gepid-upf/berimbau-esp32/main/caxixi.h

/**********************************************************************
* Written by WAVToCode
* Date:				Wed Apr 10 10:54:57 AM
* FileName:			caxixi.h
* Interleaved:		Yes
* Signed:			Yes
* No. of channels:	1
* No. of samples:	14392
* Bits/Sample:		16
**********************************************************************/

const uint32_t caxixi_length = 14392;

const int16_t caxixi_data[] = {
 -9, -2679, -722, 1820, -1052, -2216, 1130, 2875, // 0-7
1483, -2339, -2816, 1369, 775, -421, 490, 1471, // 8-15
1308, -1197, -1289, 709, -634, -2290, -438, 1622, // 16-23
1617, 1131, -1656, -1511, 1270, 232, 1076, 1445, // 24-31
-755, -719, 657, -1205, -3591, 828, 5721, -943, // 32-39
-6613, -3469, 251, 4771, 2240, -2296, 3304, 4577, // 40-47
511, -1909, -4525, 761, 8344, 1268, -6598, -2080, // 48-55
3356, 3432, -6528, -12416, -1171, 8881, 7654, -2114, // 56-63
-10416, -1733, 9952, 4211, -6298, -4386, 10158, 18213, // 64-71
1172, -10200, -6016, 1414, 5411, -7326, -12972, -827, // 72-79
9698, 2561, -13105, -18094, -3788, 12307, 17874, 10090, // 80-87
-3818, -5379, 6128, 17087, 5230, -15354, -18685, -1749, // 88-95
11127, 3568, -13002, -18067, -1662, 11987, 15213, -485, // 96-103
-7518, 2166, 7767, 9175, 1754, -12427, -6310, 11603, // 104-111
5318, -313, -1607, -864, 4625, -9109, -16903, 3754, // 112-119
14055, 778, -10999, -11145, 7126, 16884, -4923, -18462, // 120-127
1023, 20400, 15031, -5100, -24160, -12337, 16128, 12681, // 128-135
-10447, -10078, 1457, 14195, 17467, -12761, -19398, 9354, // 136-143
19190, 4248, -12628, -20710, -3382, 9069, -3041, -2253, // 144-151
-70, 1747, 10796, 3102, -5364, 5888, 6236, -6032, // 152-159
-81, 8112, 2155, -8550, -6823, 5008, 4467, -5425, // 160-167
-10925, -4550, 7412, 6031, -4954, -7164, -305, 7155, // 168-175
5011, -170, 141, 6229, 14437, 4639, -8979, -6459, // 176-183
-1706, -1893, 786, -7179, -15095, -3007, -1027, 805, // 184-191
12359, 997, -8763, 6834, 7046, 553, 4698, -2860, // 192-199
-5968, 8424, 13828, 512, -10433, -14140, -7256, 7053, // 200-207
5303, -2945, 3735, 4766, -2799, -1312, -1800, -3457, // 208-215
3213, 5648, 2101, 3135, -788, -9046, -5437, -785, // 216-223
3283, 7837, 1529, 163, 2595, -2160, -5274, -4466, // 224-231
-4587, 2612, 9347, 5459, -1384, -8128, -7694, 3405, // 232-239
10019, 3114, -7327, -4528, 4920, -514, -8646, -4258, // 240-247
5073, 7383, -331, -5284, -4044, 769, 8364, 5031, // 248-255
-1654, 1043, 1291, -978, -2179, -5084, 3956, 10897, // 256-263
-463, -4194, -1740, -4923, -2961, -1382, 140, 7903, // 264-271
1263, -7760, -4552, -5942, 821, 10355, 3710, 2887, // 272-279
1736, -1740, 5676, -691, -8164, -2082, -3065, -356, // 280-287
8329, 2299, -5475, -27, 4562, -2660, -5952, 984, // 288-295
4384, 2684, -2825, -7814, 573, 8458, -99, -5609, // 296-303
5021, 14547, 4639, -5656, -8726, -14209, -4368, 9500, // 304-311
3289, -4439, -2678, -2196, 4008, 6252, -3699, -7053, // 312-319
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
