gepid-upf/berimbau-esp32/main/moeda.h

/**********************************************************************
* Written by WAVToCode
* Date:				Wed Apr 10 10:55:23 AM
* FileName:			moeda.h
* Interleaved:		Yes
* Signed:			Yes
* No. of channels:	1
* No. of samples:	70588
* Bits/Sample:		16
**********************************************************************/

const uint32_t moeda_length = 70588;

const int16_t moeda_data[] = {
 96, 179, 249, 320, 383, 442, 493, 536, // 0-7
572, 607, 639, 660, 673, 676, 666, 653, // 8-15
639, 618, 587, 534, 477, 424, 371, 302, // 16-23
213, 117,  25, -58, -150, -242, -348, -449, // 24-31
-555, -660, -757, -853, -947, -1043, -1136, -1223, // 32-39
-1306, -1390, -1468, -1537, -1594, -1650, -1700, -1745, // 40-47
-1782, -1819, -1852, -1874, -1865, -1865, -1865, -1842, // 48-55
-1815, -1793, -1768, -1709, -1647, -1591, -1534, -1475, // 56-63
-1402, -1318, -1233, -1146, -1059, -977, -883, -793, // 64-71
-705, -613, -520, -417, -313, -220, -148, -69, // 72-79
 19, 111, 185, 253, 332, 402, 450, 501, // 80-87
545, 585, 609, 635, 652, 654, 657, 655, // 88-95
631, 607, 577, 546, 506, 458, 400, 337, // 96-103
284, 230, 155,  77, -14, -101, -193, -289, // 104-111
-374, -450, -526, -605, -680, -756, -832, -901, // 112-119
-955, -1006, -1053, -1092, -1129, -1162, -1191, -1209, // 120-127
-1210, -1210, -1215, -1215, -1197, -1170, -1144, -1105, // 128-135
-1059, -1007, -962, -908, -855, -793, -723, -650, // 136-143
-588, -503, -413, -330, -242, -152, -69,  18, // 144-151
105, 179, 261, 346, 417, 478, 543, 619, // 152-159
694, 748, 791, 831, 877, 937, 985, 1001, // 160-167
1014, 1022, 1025, 1010, 997, 988, 975, 943, // 168-175
899, 847, 787, 730, 680, 619, 547, 479, // 176-183
403, 330, 253, 168,  88,  17, -57, -129, // 184-191
-202, -267, -323, -363, -409, -458, -503, -543, // 192-199
-579, -608, -629, -628, -618, -615, -604, -571, // 200-207
-552, -524, -481, -440, -389, -333, -284, -230, // 208-215
-167, -104, -42,  41, 125, 196, 269, 344, // 216-223
412, 485, 560, 634, 712, 786, 857, 929, // 224-231
1005, 1069, 1126, 1169, 1217, 1260, 1300, 1338, // 232-239
1368, 1394, 1415, 1428, 1446, 1461, 1453, 1444, // 240-247
1431, 1416, 1391, 1367, 1322, 1277, 1241, 1195, // 248-255
1141, 1080, 1011, 947, 883, 813, 742, 657, // 256-263
574, 497, 415, 345, 275, 201, 131,  65, // 264-271
  8, -41, -84, -124, -156, -192, -214, -234, // 272-279
-244, -258, -262, -245, -219, -195, -168, -146, // 280-287
-117, -75, -40,   1,  59, 111, 156, 193, // 288-295
229, 270, 326, 390, 435, 478, 515, 555, // 296-303
597, 641, 673, 710, 747, 773, 805, 838, // 304-311
853, 869, 886, 899, 903, 907, 903, 893, // 312-319
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
